superzeldalink/STM32-Scientific-Calculator/Report/LCDScreens/int.jpeg

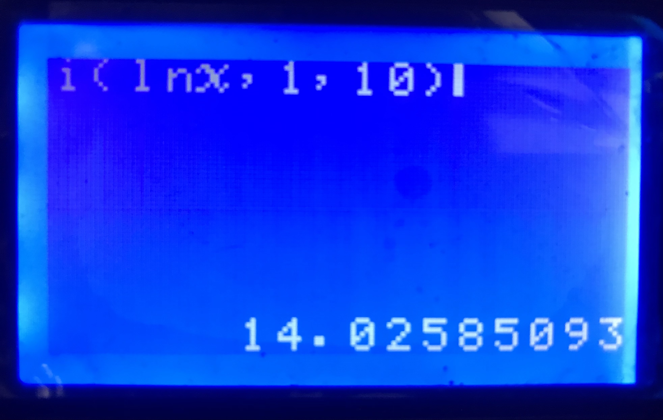
Report/LCDScreens/int.jpeg
