superzeldalink/STM32-Scientific-Calculator/Report/Software/UART_interrupt.png

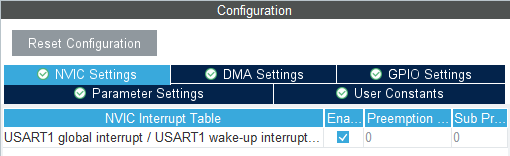
Report/Software/UART_interrupt.png
